AdamTReineke/my-ai-shed/docs/checklist-completed.md

# Shed Construction Checklist — Completed Sections

*Sections moved here from checklist.md once fully done.*

---

## Open Questions & Design Decisions — Decisions Made

- [x] **Framing**: 2x6 studs at 16" o.c., insulated
- [x] **Siding**: HardiePlank cedarmill texture, 8.25" plank with ~7" exposure, 16' on back (south), 12' on other sides
- [x] **Siding finish**: Primed, field-painted to match house
- [x] **Size**: 16' x 12' (192 sf, under 200 sf threshold)
- [x] **Permitting**: No structural permit; electrical permitted separately
- [x] **HVAC**: DIY mini-split and/or dehumidifier
- [x] **Location**: Redmond, WA (climate zone 4C, marine)
- [x] **Design life**: 50 years
- [x] **Primary use**: Storage (all walls clear, minimal electrical)
- [x] **Wall covering**: 1/2" CDX plywood (from Dunn order), painted if needed
- [x] **Windows**: None
- [x] **Door**: Single wood man door (already purchased, measurements TBD), north wall east end
- [x] **Floor insulation**: Polyiso rigid foam between joists (Rmax ThermoSheath-3, 3" R-20.3, purchased)
- [x] **Roof insulation**: At roof plane (unvented/hot roof)
- [x] **Electrical**: Underground trench (DIY), 2 circuits (mini-split dedicated + lights/outlets), electrician for wiring. Two-switch design: one for lights, one master kill switch.
- [x] **Pier skirting**: None for now
- [x] **Exterior colors**: Matching house (already selected)
- [x] **Access**: Steps with landing at door (door opens inward)

---

## 1. Site Preparation & Layout

### Survey & Marking
- [x] Verify property setbacks with Redmond requirements
- [x] Mark 16' x 12' footprint corners (16' E-W, 12' N-S)
- [x] Mark 6 pier center locations (1', 8', 15' from east edge on each beam line)
- [x] Verify beam lines at 1.5' and 10.5' from north edge
- [x] Check diagonals for square
- [x] Set up batter boards for string lines
- [x] Establish elevation reference point (east = high ground)
- [x] Survey ground slope (expect ~28" drop east to west)
- [x] Calculate pier top elevations to achieve level beams

### Site Clearing
- [x] Remove vegetation from footprint + 2' perimeter
- [x] Remove roots that could affect pier locations
- [x] Grade for drainage away from shed location

---

## 2. Concrete Piers (6 total)

### Excavation
- [x] Dig 4 corner pier holes: wide enough for BigFoot 25.5" base × 24" deep
- [x] Dig 2 center pier holes: wide enough for BigFoot 29.5" base × 24" deep
- [x] Verify depth below 12" frost line
- [x] Level and compact bottom of each hole (BigFoot base must sit on undisturbed/compacted soil)
- [x] Check for groundwater intrusion

**Note:** East and center piers rise to beam level — beam sits directly on concrete via saddle hardware (no posts). Only west piers are short and use 6×6 posts. Verify pier top elevations at east/center positions match beam bottom elevation. See `shed/concrete.js` for as-built measurements.

### Forming & Pouring
- [x] Check weather - need 48+ hours without rain/freeze
- [x] Set BigFoot form feet in holes, level on compacted soil
- [x] Attach sonotubes to BigFoot bases (10" for corners, 12" for centers; cut tubes to length)
  <actual dimensions as-poured are recorded in concrete.js>
- [x] Set tube forms plumb
- [x] Level form tops at correct elevations (accounting for 28" slope)
- [x] Brace forms securely
- [x] East and center pier forms taller (beam sits directly on saddle at these 4 positions)
- [x] Cut GFRP rebar to length (hacksaw — wear dust mask for fiberglass dust)
- [x] Insert one vertical GFRP bar per pier partway through pour, adjust to keep centered
- [x] Mix/order 4000 psi concrete
- [x] Pour and vibrate to consolidate
- [x] Screed tops flat and level
- [x] Leave smooth for post-install anchors
- [x] Cover and protect from rain
- [x] Cure minimum 7 days before loading

### Post-Pour
- [x] Strip tube forms
- [x] Backfill around piers
- [x] Compact backfill
