AdamTReineke/my-ai-shed/docs/10-stairs.md

# 10 — Stairs & Landing

## Entry Landing

The door is on the north wall at the east end and opens inward. Since it opens inward, the landing doesn't need to be as deep as for an outswing door, but **36" deep minimum** is still needed for comfortable entry.

The site slopes ~28" east to west, so the east end (door side) is closest to grade. The steps and landing may only need 1-2 risers depending on final pier/floor elevation — confirm after floor framing is complete.

## Design TBD

*Details to be finalized once floor elevation is established.*

- [ ] Measure actual floor-to-grade height at door
- [ ] Determine number of steps needed
- [ ] Design landing platform (~36" deep × door width minimum)
- [ ] Select materials (PT lumber, composite decking, or concrete pad)
- [ ] Install stringers and landing before door installation
