AdamTReineke/my-ai-shed/images.md

# Shed Model Renders

## Table of Contents

### Progressive Assembly
- [Foundation — Concrete piers and post bases](#foundation--concrete-piers-and-post-bases)
- [Floor Framing — Posts, beams, joists, rim joists, blocking, and hurricane ties](#floor-framing--posts-beams-joists-rim-joists-blocking-and-hurricane-ties)
- [Floor Deck — Floor framing with 3/4" AdvanTech decking](#floor-deck--floor-framing-with-34-advantech-decking)
- [Walls — Full floor system with wall framing](#walls--full-floor-system-with-wall-framing)
- [Full Framing — Floor, walls, trusses, and ladder framing](#full-framing--floor-walls-trusses-and-ladder-framing)
- [Wall Cladding — OSB sheathing, furring strips, and HardiePlank siding](#wall-cladding--osb-sheathing-furring-strips-and-hardieplank-siding)
- [Roof Framing — Complete floor and wall system with queen-post trusses](#roof-framing--complete-floor-and-wall-system-with-queen-post-trusses)
- [Complete — Finished shed with all structural and cladding layers](#complete--finished-shed-with-all-structural-and-cladding-layers)

### Isolation Views
- [Concrete piers only](#concrete-piers-only)
- [Piers, post bases, and post stubs (close-up)](#piers-post-bases-and-post-stubs-close-up)
- [Piers and post bases — foundation system](#piers-and-post-bases--foundation-system)
- [Posts on their piers and bases](#posts-on-their-piers-and-bases)
- [Built-up beams viewed from the east side](#built-up-beams-viewed-from-the-east-side)
- [Posts-and-beams skeleton](#posts-and-beams-skeleton)
- [Floor joists spanning between beams](#floor-joists-spanning-between-beams)
- [Joists and rim joists forming the floor frame perimeter](#joists-and-rim-joists-forming-the-floor-frame-perimeter)
- [Mid-span blocking viewed from below](#mid-span-blocking-viewed-from-below)
- [Hurricane tie detail (close-up, east end)](#hurricane-tie-detail-close-up-east-end)
- [Complete floor framing system](#complete-floor-framing-system)
- [Wall stud framing on the floor deck](#wall-stud-framing-on-the-floor-deck)
- [Wall framing with OSB sheathing](#wall-framing-with-osb-sheathing)
- [OSB sheathing with vertical furring strips (rainscreen gap)](#osb-sheathing-with-vertical-furring-strips-rainscreen-gap)
- [Furring with HardiePlank lap siding](#furring-with-hardieplank-lap-siding)
- [Complete wall cladding — OSB, furring, and siding](#complete-wall-cladding--osb-furring-and-siding)
- [Queen-post trusses on the walls](#queen-post-trusses-on-the-walls)
- [Trusses with gable-end ladder framing](#trusses-with-gable-end-ladder-framing)
- [Complete roof framing system](#complete-roof-framing-system)
- [Roof sheathing (Zip System panels)](#roof-sheathing-zip-system-panels)

## Progressive Assembly

**Foundation — Concrete piers and post bases**
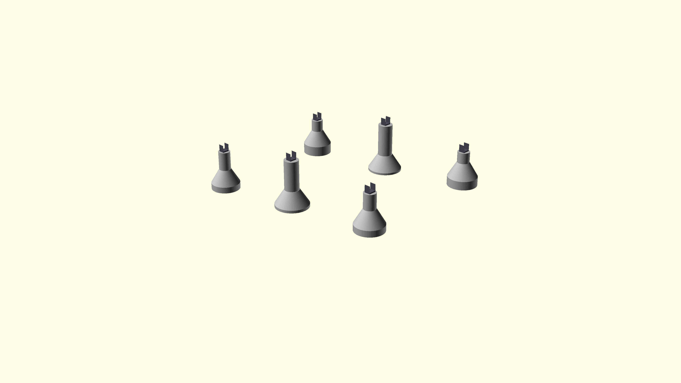
[picture p3: renders/01-foundation.png]
Foundation


**Floor Framing — Posts, beams, joists, rim joists, blocking, and hurricane ties**
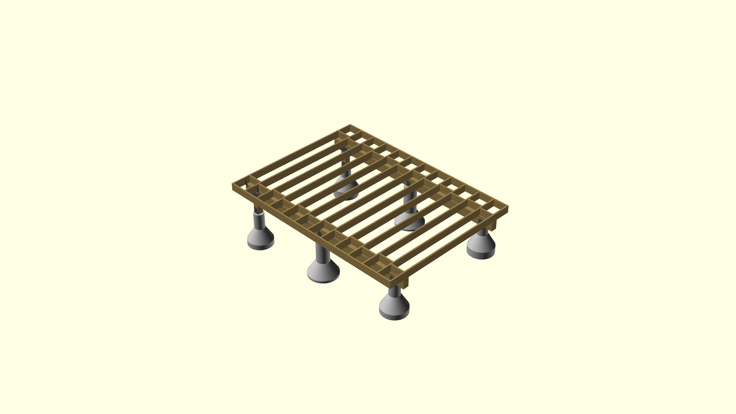
[picture p4: renders/02-floor-framing.png]
Floor Framing


**Floor Deck — Floor framing with 3/4" AdvanTech decking**
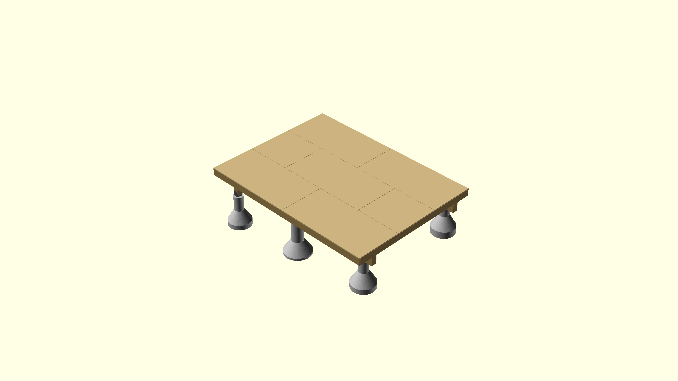
[picture p5: renders/03-floor-deck.png]
Floor Deck


**Walls — Full floor system with wall framing**
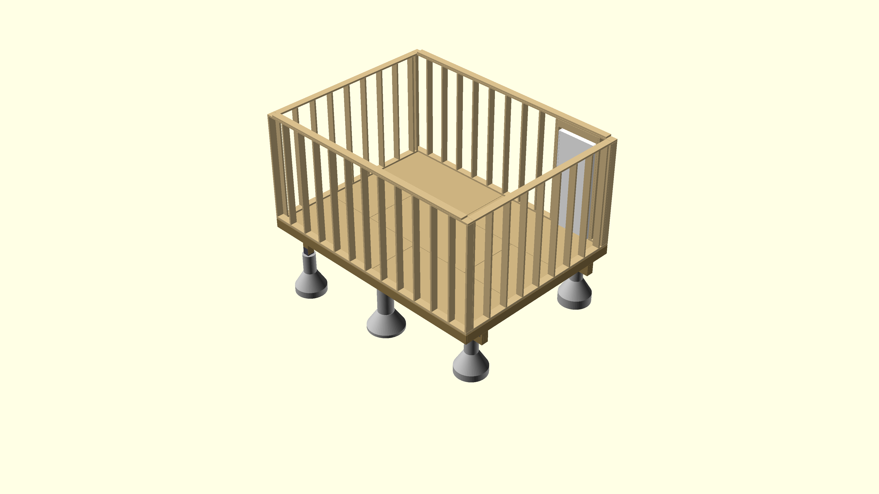
[picture p6: renders/04-walls.png]
Walls


**Full Framing — Floor, walls, trusses, and ladder framing**
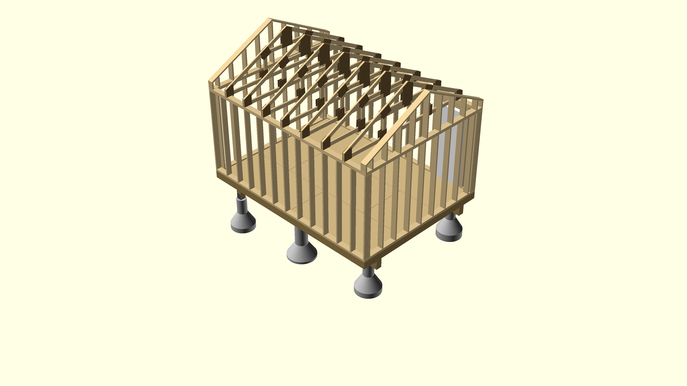
[picture p7: renders/05-full-framing.png]
Full Framing


**Wall Cladding — OSB sheathing, furring strips, and HardiePlank siding**
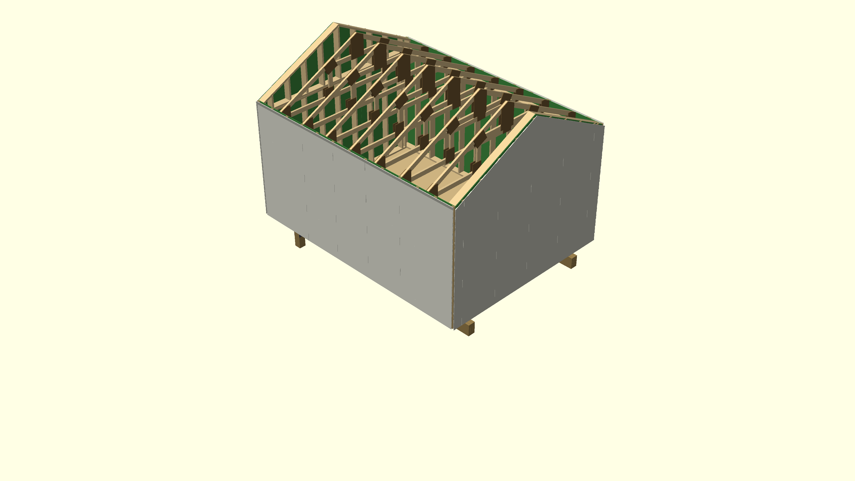
[picture p8: renders/06-cladding.png]
Wall Cladding


**Roof Framing — Complete floor and wall system with queen-post trusses**
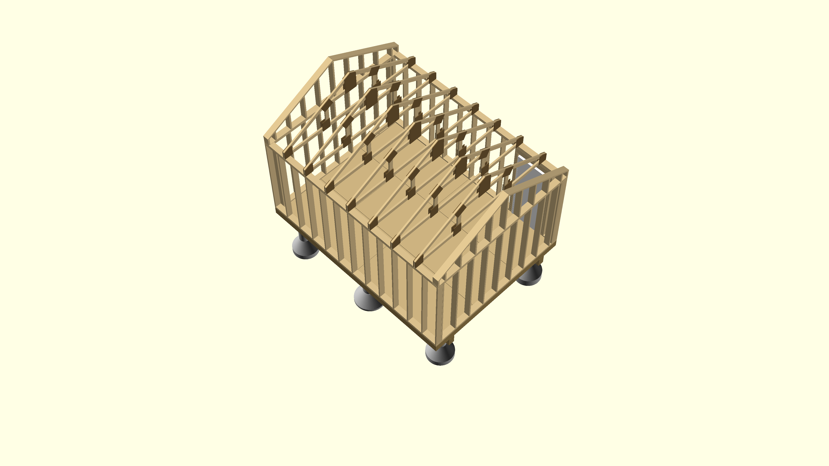
[picture p9: renders/07-trusses.png]


**Complete — Finished shed with all structural and cladding layers**
Complete

## Isolation Views

**Concrete piers only**
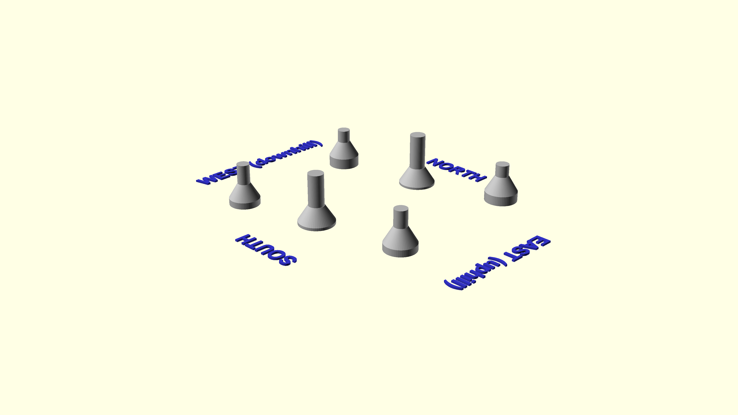
[picture p10: renders/iso-pier.png]
Pier


**Piers, post bases, and post stubs (close-up)**
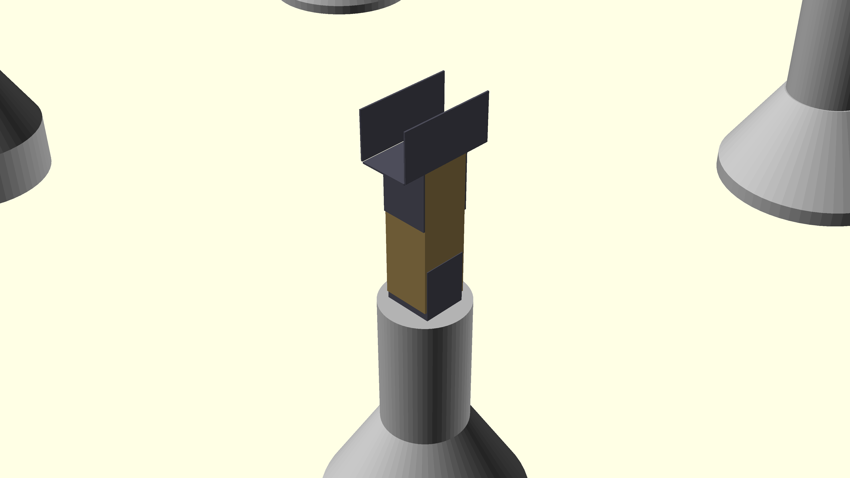
[picture p11: renders/iso-post-base.png]
Post Base


**Piers and post bases — foundation system**
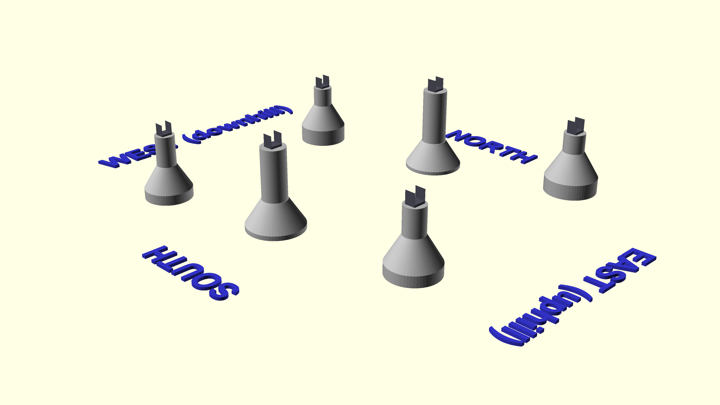
[picture p12: renders/iso-foundation.png]
Foundation


**Posts on their piers and bases**
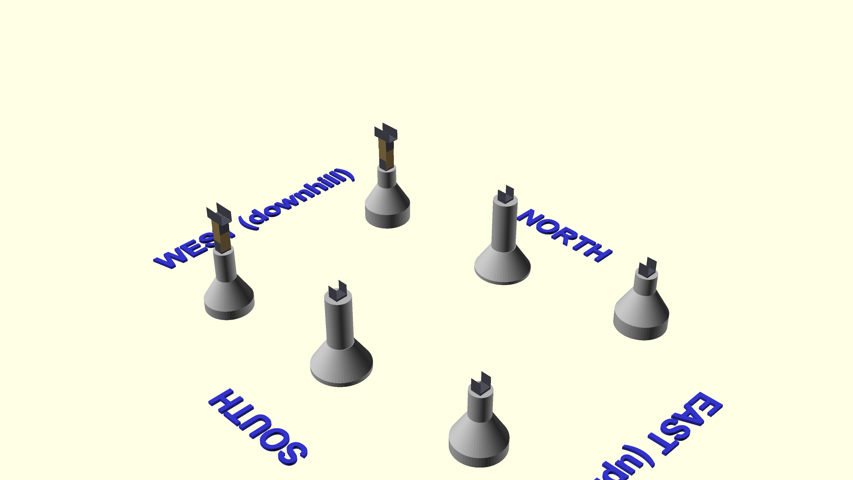
[picture p13: renders/iso-post.png]
Post


**Built-up beams viewed from the east side**
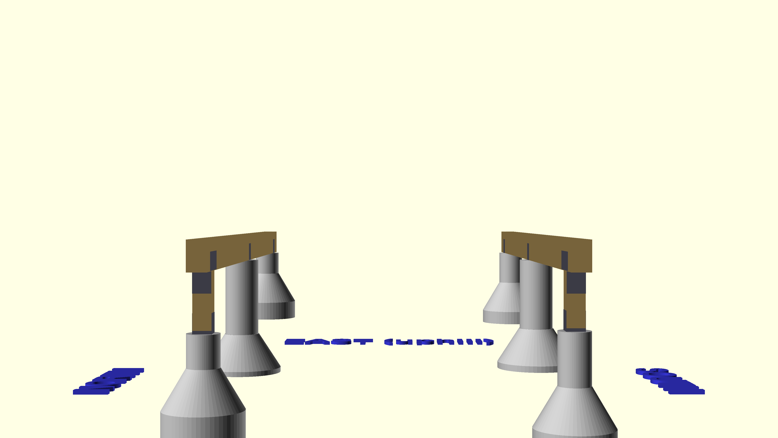
[picture p14: renders/iso-beam.png]
Beam


**Posts-and-beams skeleton**
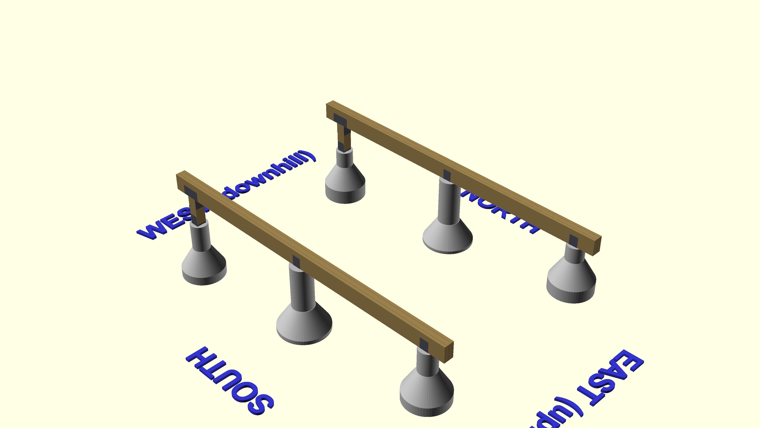
[picture p15: renders/iso-posts-and-beams.png]
Posts and Beams


**Joists and rim joists forming the floor frame perimeter**
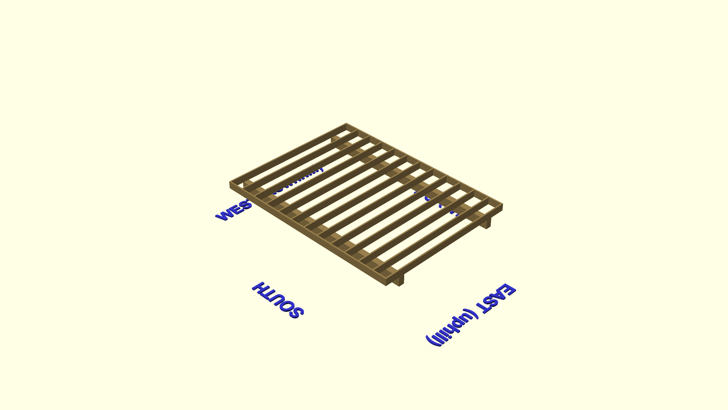
[picture p16: renders/iso-rim-joist.png]
Rim Joist


**Mid-span blocking viewed from below**
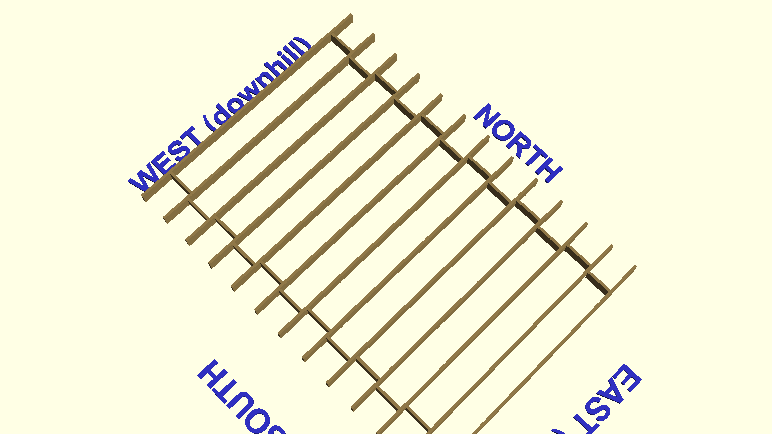
[picture p17: renders/iso-blocking.png]
Blocking


**Hurricane tie detail (close-up, east end)**
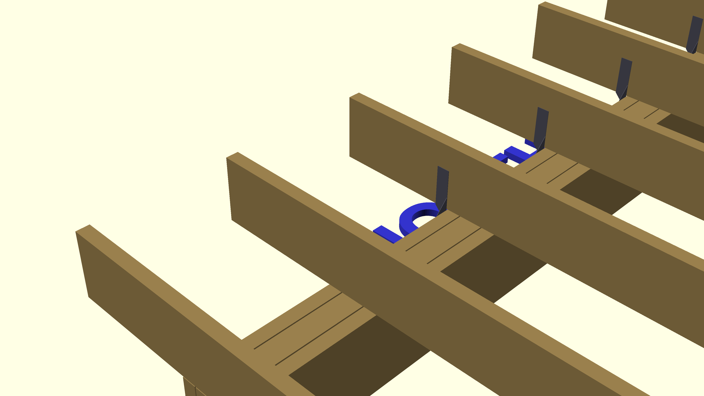
[picture p18: renders/iso-hurricane-tie.png]
Hurricane Tie


**Complete floor framing system**
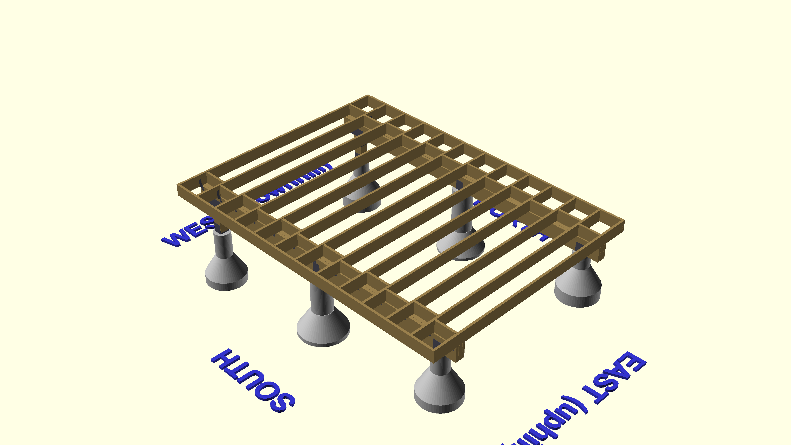
[picture p19: renders/iso-floor-framing.png]
Floor Framing


**Wall stud framing on the floor deck**
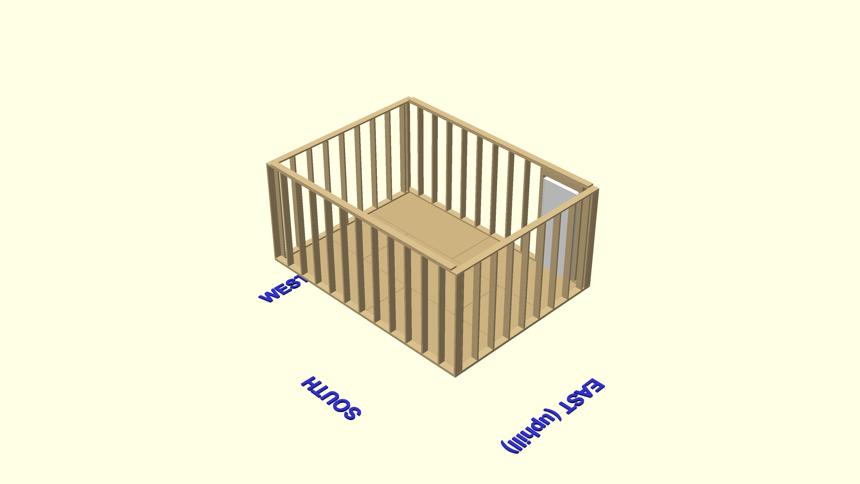
[picture p20: renders/iso-wall-framing.png]
Wall Framing


**Wall framing with OSB sheathing**
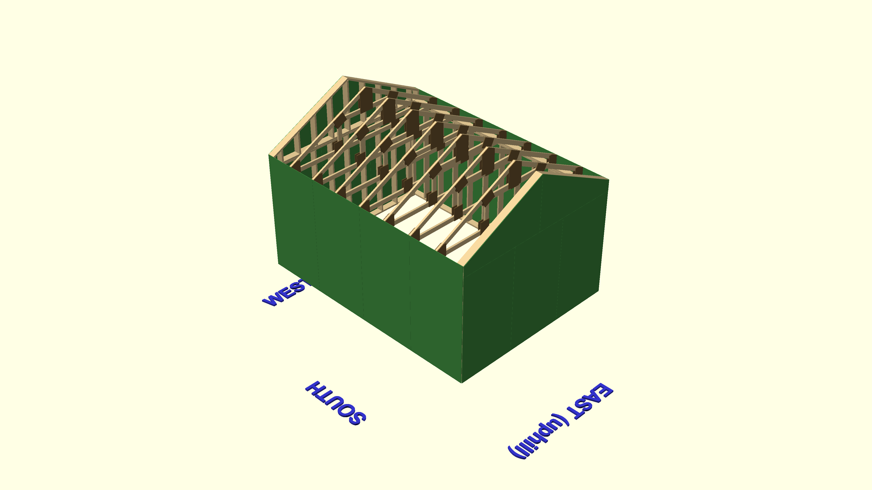
[picture p21: renders/iso-osb.png]
OSB


**OSB sheathing with vertical furring strips (rainscreen gap)**
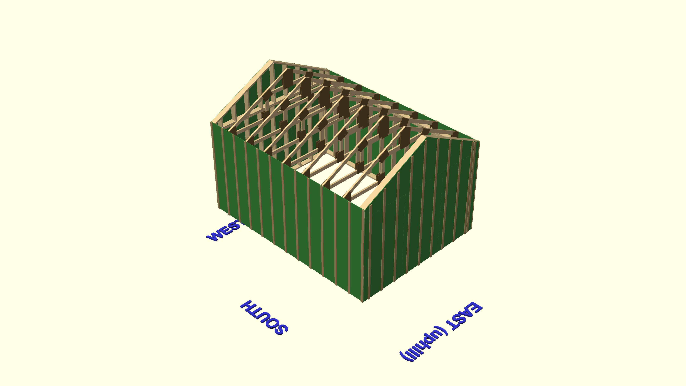
[picture p22: renders/iso-furring.png]
Furring


**Furring with HardiePlank lap siding**
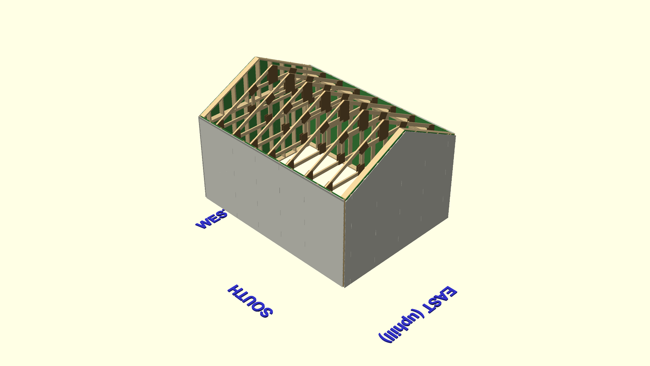
[picture p23: renders/iso-siding.png]
Siding


**Complete wall cladding — OSB, furring, and siding**
Cladding

**Queen-post trusses on the walls**
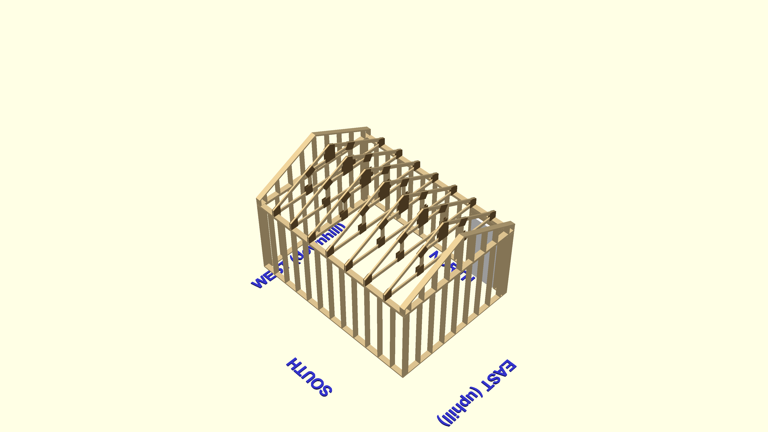
[picture p24: renders/iso-truss.png]
Truss


**Trusses with gable-end ladder framing**
Ladder Framing

**Complete roof framing system**
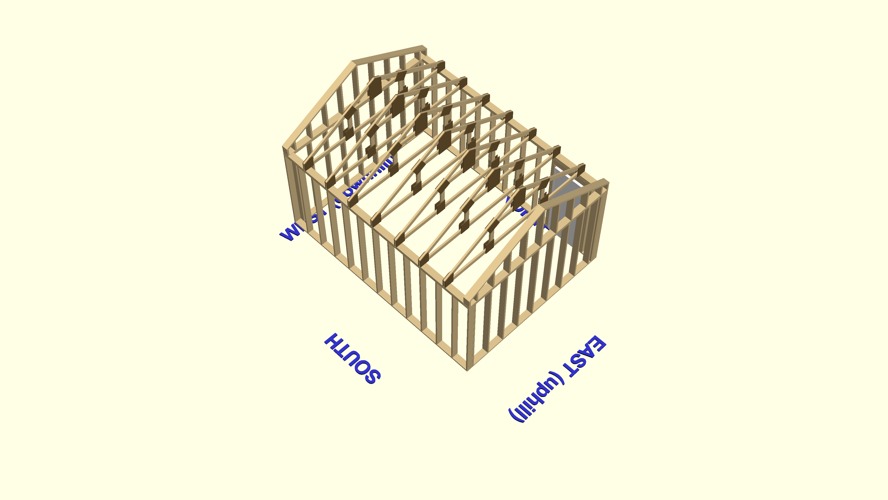
[picture p25: renders/iso-roof-framing.png]
Roof Framing


**Roof sheathing (Zip System panels)**
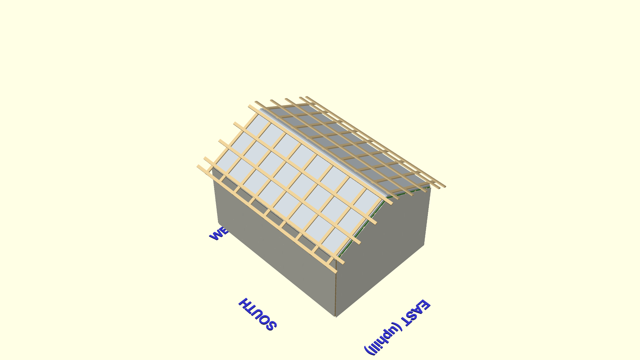
[picture p26: renders/iso-roof-sheathing.png]
Roof Sheathing
