AdamTReineke/my-ai-shed/screenshots/image.png

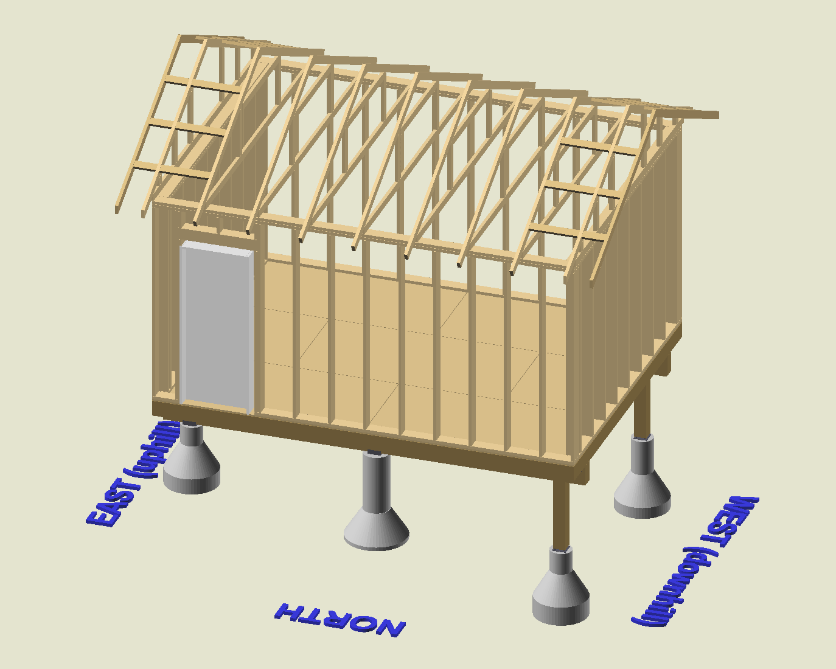
screenshots/image.png
