AdamTReineke/my-ai-shed/model/siding_data.scad

// Generated by tools/siding-cuts.js — do not edit
// 141 pieces, 77 stock planks

south_siding = [
    [[0.125, 47.9375], [48.0625, 191.875]],  // course 0
    [[0.125, 79.9375], [80.0625, 191.875]],  // course 1
    [[0.125, 111.9375], [112.0625, 191.875]],  // course 2
    [[0.125, 143.9375], [144.0625, 191.875]],  // course 3
    [[0.125, 47.9375], [48.0625, 191.875]],  // course 4
    [[0.125, 79.9375], [80.0625, 191.875]],  // course 5
    [[0.125, 111.9375], [112.0625, 191.875]],  // course 6
    [[0.125, 143.9375], [144.0625, 191.875]],  // course 7
    [[0.125, 47.9375], [48.0625, 191.875]],  // course 8
    [[0.125, 79.9375], [80.0625, 191.875]],  // course 9
    [[0.125, 111.9375], [112.0625, 191.875]],  // course 10
    [[0.125, 143.9375], [144.0625, 191.875]],  // course 11
    [[0.125, 47.9375], [48.0625, 191.875]],  // course 12
    [[0.125, 79.9375], [80.0625, 191.875]],  // course 13
    [[0.125, 111.9375], [112.0625, 191.875]],  // course 14
    [[0.125, 143.9375], [144.0625, 191.875]]  // course 15
];

north_siding = [
    [[0.125, 47.9375], [48.0625, 145.5], [178.5, 191.875]],  // course 0
    [[0.125, 79.9375], [80.0625, 145.5], [178.5, 191.875]],  // course 1
    [[0.125, 111.9375], [112.0625, 145.5], [178.5, 191.875]],  // course 2
    [[0.125, 127.9375], [128.0625, 145.5], [178.5, 191.875]],  // course 3
    [[0.125, 47.9375], [48.0625, 145.5], [178.5, 191.875]],  // course 4
    [[0.125, 79.9375], [80.0625, 145.5], [178.5, 191.875]],  // course 5
    [[0.125, 111.9375], [112.0625, 145.5], [178.5, 191.875]],  // course 6
    [[0.125, 127.9375], [128.0625, 145.5], [178.5, 191.875]],  // course 7
    [[0.125, 47.9375], [48.0625, 145.5], [178.5, 191.875]],  // course 8
    [[0.125, 79.9375], [80.0625, 145.5], [178.5, 191.875]],  // course 9
    [[0.125, 111.9375], [112.0625, 145.5], [178.5, 191.875]],  // course 10
    [[0.125, 127.9375], [128.0625, 145.5], [178.5, 191.875]],  // course 11
    [[0.125, 47.9375], [48.0625, 145.5], [178.5, 191.875]],  // course 12
    [[0.125, 79.9375], [80.0625, 191.875]],  // course 13
    [[0.125, 111.9375], [112.0625, 191.875]],  // course 14
    [[0.125, 143.1875], [143.3125, 191.875]]  // course 15
];

east_siding = [
    [[0.125, 7.6875], [7.8125, 146.875]],  // course 0
    [[0.125, 39.6875], [39.8125, 146.875]],  // course 1
    [[0.125, 71.6875], [71.8125, 146.875]],  // course 2
    [[0.125, 103.6875], [103.8125, 146.875]],  // course 3
    [[0.125, 135.6875], [135.8125, 146.875]],  // course 4
    [[0.125, 7.6875], [7.8125, 146.875]],  // course 5
    [[0.125, 39.6875], [39.8125, 146.875]],  // course 6
    [[0.125, 71.6875], [71.8125, 146.875]],  // course 7
    [[0.125, 103.6875], [103.8125, 146.875]],  // course 8
    [[0.125, 135.6875], [135.8125, 146.875]],  // course 9
    [[0.125, 7.6875], [7.8125, 146.875]],  // course 10
    [[0.125, 39.6875], [39.8125, 146.875]],  // course 11
    [[0.125, 71.6875], [71.8125, 146.875]],  // course 12
    [[0.125, 103.6875], [103.8125, 146.875]],  // course 13
    [[0.125, 135.6875], [135.8125, 146.875]],  // course 14
    [[0.125, 7.6875], [7.8125, 146.875]]  // course 15
];

west_siding = [
    [[0.125, 7.6875], [7.8125, 146.875]],  // course 0
    [[0.125, 39.6875], [39.8125, 146.875]],  // course 1
    [[0.125, 71.6875], [71.8125, 146.875]],  // course 2
    [[0.125, 103.6875], [103.8125, 146.875]],  // course 3
    [[0.125, 135.6875], [135.8125, 146.875]],  // course 4
    [[0.125, 7.6875], [7.8125, 146.875]],  // course 5
    [[0.125, 39.6875], [39.8125, 146.875]],  // course 6
    [[0.125, 71.6875], [71.8125, 146.875]],  // course 7
    [[0.125, 103.6875], [103.8125, 146.875]],  // course 8
    [[0.125, 135.6875], [135.8125, 146.875]],  // course 9
    [[0.125, 7.6875], [7.8125, 146.875]],  // course 10
    [[0.125, 39.6875], [39.8125, 146.875]],  // course 11
    [[0.125, 71.6875], [71.8125, 146.875]],  // course 12
    [[0.125, 103.6875], [103.8125, 146.875]],  // course 13
    [[0.125, 135.6875], [135.8125, 146.875]],  // course 14
    [[0.125, 7.6875], [7.8125, 146.875]]  // course 15
];
