AdamTReineke/my-ai-shed/model/truss_data.scad

// Auto-generated by generate-truss-data.js — do not edit by hand
// Run: node shed/model/generate-truss-data.js

// === CUT LIST (per truss) ===
// Bottom Chord: 2x4 x 144.00" (12'-0.0")
// South Rafter: 2x4 x 80.5" (6'-8.5") - plumb cuts both ends at 26.6°
// North Rafter: 2x4 x 80.5" (6'-8.5") - plumb cuts both ends at 26.6°
// South Queen Post: 2x4 x 22.3" (1'-10.3") - angle cut top at 26.6°
// North Queen Post: 2x4 x 22.3" (1'-10.3") - angle cut top at 26.6°
// Straining Beam: 2x4 x 48.00" (4'-0.0")
// Peak Gusset: 1/2" plywood, 12" x 19.4" pentagon, qty 2 (one each side)
// Queen Post Top Gusset: 1/2" plywood, 10" x 8" rectangle (roof-aligned), qty 4 (2 per joint, 2 joints)
// Queen Post Bottom Gusset: 1/2" plywood, 10" x 8" rectangle, qty 4 (2 per joint, 2 joints)
// Eave Gusset: 1/2" plywood, 10" x 8" rectangle, qty 4 (2 per joint, 2 joints)

module truss_bottom_chord() {
    polyhedron(
        points = [
            [-0.75, 0.125, 0],
            [-0.75, 143.875, 0],
            [-0.75, 143.875, 3.5],
            [-0.75, 0.125, 3.5],
            [0.75, 0.125, 0],
            [0.75, 143.875, 0],
            [0.75, 143.875, 3.5],
            [0.75, 0.125, 3.5]
        ],
        faces = [
            [0,1,2,3],
            [7,6,5,4],
            [0,4,5,1],
            [2,6,7,3],
            [1,5,6,2],
            [0,3,7,4]
        ]
    );
}

module truss_south_rafter() {
    polyhedron(
        points = [
            [-0.75, 0, 3.5],
            [-0.75, 71.9375, 39.4688],
            [-0.75, 71.9375, 43.3819],
            [-0.75, 0, 7.4131],
            [0.75, 0, 3.5],
            [0.75, 71.9375, 39.4688],
            [0.75, 71.9375, 43.3819],
            [0.75, 0, 7.4131]
        ],
        faces = [
            [0,1,2,3],
            [7,6,5,4],
            [0,4,5,1],
            [2,6,7,3],
            [1,5,6,2],
            [0,3,7,4]
        ]
    );
}

module truss_north_rafter() {
    polyhedron(
        points = [
            [-0.75, 72.0625, 39.4688],
            [-0.75, 144, 3.5],
            [-0.75, 144, 7.4131],
            [-0.75, 72.0625, 43.3819],
            [0.75, 72.0625, 39.4688],
            [0.75, 144, 3.5],
            [0.75, 144, 7.4131],
            [0.75, 72.0625, 43.3819]
        ],
        faces = [
            [0,1,2,3],
            [7,6,5,4],
            [0,4,5,1],
            [2,6,7,3],
            [1,5,6,2],
            [0,3,7,4]
        ]
    );
}

module truss_south_queen_post() {
    polyhedron(
        points = [
            [-0.75, 44.5, 3.625],
            [-0.75, 48, 3.625],
            [-0.75, 48, 27.375],
            [-0.75, 44.5, 25.625],
            [0.75, 44.5, 3.625],
            [0.75, 48, 3.625],
            [0.75, 48, 27.375],
            [0.75, 44.5, 25.625]
        ],
        faces = [
            [0,1,2,3],
            [7,6,5,4],
            [0,4,5,1],
            [2,6,7,3],
            [1,5,6,2],
            [0,3,7,4]
        ]
    );
}

module truss_north_queen_post() {
    polyhedron(
        points = [
            [-0.75, 96, 3.625],
            [-0.75, 99.5, 3.625],
            [-0.75, 99.5, 25.625],
            [-0.75, 96, 27.375],
            [0.75, 96, 3.625],
            [0.75, 99.5, 3.625],
            [0.75, 99.5, 25.625],
            [0.75, 96, 27.375]
        ],
        faces = [
            [0,1,2,3],
            [7,6,5,4],
            [0,4,5,1],
            [2,6,7,3],
            [1,5,6,2],
            [0,3,7,4]
        ]
    );
}

module truss_straining_beam() {
    polyhedron(
        points = [
            [-0.75, 48.125, 24],
            [-0.75, 95.875, 24],
            [-0.75, 95.875, 27.5],
            [-0.75, 48.125, 27.5],
            [0.75, 48.125, 24],
            [0.75, 95.875, 24],
            [0.75, 95.875, 27.5],
            [0.75, 48.125, 27.5]
        ],
        faces = [
            [0,1,2,3],
            [7,6,5,4],
            [0,4,5,1],
            [2,6,7,3],
            [1,5,6,2],
            [0,3,7,4]
        ]
    );
}

module truss_peak_gusset() {
    polyhedron(
        points = [
            [-1.25, 66, 24],
            [-1.25, 78, 24],
            [-1.25, 78, 40.4131],
            [-1.25, 72, 43.4131],
            [-1.25, 66, 40.4131],
            [-0.75, 66, 24],
            [-0.75, 78, 24],
            [-0.75, 78, 40.4131],
            [-0.75, 72, 43.4131],
            [-0.75, 66, 40.4131]
        ],
        faces = [
            [0,1,2,3,4],
            [9,8,7,6,5],
            [0,1,6,5],
            [1,2,7,6],
            [2,3,8,7],
            [3,4,9,8],
            [4,0,5,9]
        ]
    );
    polyhedron(
        points = [
            [0.75, 66, 24],
            [0.75, 78, 24],
            [0.75, 78, 40.4131],
            [0.75, 72, 43.4131],
            [0.75, 66, 40.4131],
            [1.25, 66, 24],
            [1.25, 78, 24],
            [1.25, 78, 40.4131],
            [1.25, 72, 43.4131],
            [1.25, 66, 40.4131]
        ],
        faces = [
            [0,1,2,3,4],
            [9,8,7,6,5],
            [0,1,6,5],
            [1,2,7,6],
            [2,3,8,7],
            [3,4,9,8],
            [4,0,5,9]
        ]
    );
}

module truss_south_qp_top_gusset() {
    polyhedron(
        points = [
            [-1.25, 43.7903, 20.364],
            [-1.25, 52.7346, 24.8361],
            [-1.25, 49.1569, 31.9916],
            [-1.25, 40.2126, 27.5194],
            [-0.75, 43.7903, 20.364],
            [-0.75, 52.7346, 24.8361],
            [-0.75, 49.1569, 31.9916],
            [-0.75, 40.2126, 27.5194]
        ],
        faces = [
            [0,1,2,3],
            [7,6,5,4],
            [0,1,5,4],
            [1,2,6,5],
            [2,3,7,6],
            [3,0,4,7]
        ]
    );
    polyhedron(
        points = [
            [0.75, 43.7903, 20.364],
            [0.75, 52.7346, 24.8361],
            [0.75, 49.1569, 31.9916],
            [0.75, 40.2126, 27.5194],
            [1.25, 43.7903, 20.364],
            [1.25, 52.7346, 24.8361],
            [1.25, 49.1569, 31.9916],
            [1.25, 40.2126, 27.5194]
        ],
        faces = [
            [0,1,2,3],
            [7,6,5,4],
            [0,1,5,4],
            [1,2,6,5],
            [2,3,7,6],
            [3,0,4,7]
        ]
    );
}

module truss_north_qp_top_gusset() {
    polyhedron(
        points = [
            [-1.25, 100.2097, 20.364],
            [-1.25, 91.2654, 24.8361],
            [-1.25, 94.8431, 31.9916],
            [-1.25, 103.7874, 27.5194],
            [-0.75, 100.2097, 20.364],
            [-0.75, 91.2654, 24.8361],
            [-0.75, 94.8431, 31.9916],
            [-0.75, 103.7874, 27.5194]
        ],
        faces = [
            [0,1,2,3],
            [7,6,5,4],
            [0,1,5,4],
            [1,2,6,5],
            [2,3,7,6],
            [3,0,4,7]
        ]
    );
    polyhedron(
        points = [
            [0.75, 100.2097, 20.364],
            [0.75, 91.2654, 24.8361],
            [0.75, 94.8431, 31.9916],
            [0.75, 103.7874, 27.5194],
            [1.25, 100.2097, 20.364],
            [1.25, 91.2654, 24.8361],
            [1.25, 94.8431, 31.9916],
            [1.25, 103.7874, 27.5194]
        ],
        faces = [
            [0,1,2,3],
            [7,6,5,4],
            [0,1,5,4],
            [1,2,6,5],
            [2,3,7,6],
            [3,0,4,7]
        ]
    );
}

module truss_south_qp_bottom_gusset() {
    polyhedron(
        points = [
            [-1.25, 40, 0],
            [-1.25, 48, 0],
            [-1.25, 48, 10],
            [-1.25, 40, 10],
            [-0.75, 40, 0],
            [-0.75, 48, 0],
            [-0.75, 48, 10],
            [-0.75, 40, 10]
        ],
        faces = [
            [0,1,2,3],
            [7,6,5,4],
            [0,1,5,4],
            [1,2,6,5],
            [2,3,7,6],
            [3,0,4,7]
        ]
    );
    polyhedron(
        points = [
            [0.75, 40, 0],
            [0.75, 48, 0],
            [0.75, 48, 10],
            [0.75, 40, 10],
            [1.25, 40, 0],
            [1.25, 48, 0],
            [1.25, 48, 10],
            [1.25, 40, 10]
        ],
        faces = [
            [0,1,2,3],
            [7,6,5,4],
            [0,1,5,4],
            [1,2,6,5],
            [2,3,7,6],
            [3,0,4,7]
        ]
    );
}

module truss_north_qp_bottom_gusset() {
    polyhedron(
        points = [
            [-1.25, 96, 0],
            [-1.25, 104, 0],
            [-1.25, 104, 10],
            [-1.25, 96, 10],
            [-0.75, 96, 0],
            [-0.75, 104, 0],
            [-0.75, 104, 10],
            [-0.75, 96, 10]
        ],
        faces = [
            [0,1,2,3],
            [7,6,5,4],
            [0,1,5,4],
            [1,2,6,5],
            [2,3,7,6],
            [3,0,4,7]
        ]
    );
    polyhedron(
        points = [
            [0.75, 96, 0],
            [0.75, 104, 0],
            [0.75, 104, 10],
            [0.75, 96, 10],
            [1.25, 96, 0],
            [1.25, 104, 0],
            [1.25, 104, 10],
            [1.25, 96, 10]
        ],
        faces = [
            [0,1,2,3],
            [7,6,5,4],
            [0,1,5,4],
            [1,2,6,5],
            [2,3,7,6],
            [3,0,4,7]
        ]
    );
}

module truss_south_eave_gusset() {
    polyhedron(
        points = [
            [-1.25, 0, 0],
            [-1.25, 8, 0],
            [-1.25, 8, 10],
            [-1.25, 5.1738, 10],
            [-1.25, 0, 7.4131],
            [-0.75, 0, 0],
            [-0.75, 8, 0],
            [-0.75, 8, 10],
            [-0.75, 5.1738, 10],
            [-0.75, 0, 7.4131]
        ],
        faces = [
            [0,1,2,3,4],
            [9,8,7,6,5],
            [0,1,6,5],
            [1,2,7,6],
            [2,3,8,7],
            [3,4,9,8],
            [4,0,5,9]
        ]
    );
    polyhedron(
        points = [
            [0.75, 0, 0],
            [0.75, 8, 0],
            [0.75, 8, 10],
            [0.75, 5.1738, 10],
            [0.75, 0, 7.4131],
            [1.25, 0, 0],
            [1.25, 8, 0],
            [1.25, 8, 10],
            [1.25, 5.1738, 10],
            [1.25, 0, 7.4131]
        ],
        faces = [
            [0,1,2,3,4],
            [9,8,7,6,5],
            [0,1,6,5],
            [1,2,7,6],
            [2,3,8,7],
            [3,4,9,8],
            [4,0,5,9]
        ]
    );
}

module truss_north_eave_gusset() {
    polyhedron(
        points = [
            [-1.25, 136, 0],
            [-1.25, 144, 0],
            [-1.25, 144, 7.4131],
            [-1.25, 138.8262, 10],
            [-1.25, 136, 10],
            [-0.75, 136, 0],
            [-0.75, 144, 0],
            [-0.75, 144, 7.4131],
            [-0.75, 138.8262, 10],
            [-0.75, 136, 10]
        ],
        faces = [
            [0,1,2,3,4],
            [9,8,7,6,5],
            [0,1,6,5],
            [1,2,7,6],
            [2,3,8,7],
            [3,4,9,8],
            [4,0,5,9]
        ]
    );
    polyhedron(
        points = [
            [0.75, 136, 0],
            [0.75, 144, 0],
            [0.75, 144, 7.4131],
            [0.75, 138.8262, 10],
            [0.75, 136, 10],
            [1.25, 136, 0],
            [1.25, 144, 0],
            [1.25, 144, 7.4131],
            [1.25, 138.8262, 10],
            [1.25, 136, 10]
        ],
        faces = [
            [0,1,2,3,4],
            [9,8,7,6,5],
            [0,1,6,5],
            [1,2,7,6],
            [2,3,8,7],
            [3,4,9,8],
            [4,0,5,9]
        ]
    );
}
